nimitvijayvargee/keyboardv2/KICAD/keyboardv2.kicad_sch

## KiCad design KICAD/keyboardv2.kicad_sch (2025-06-17)

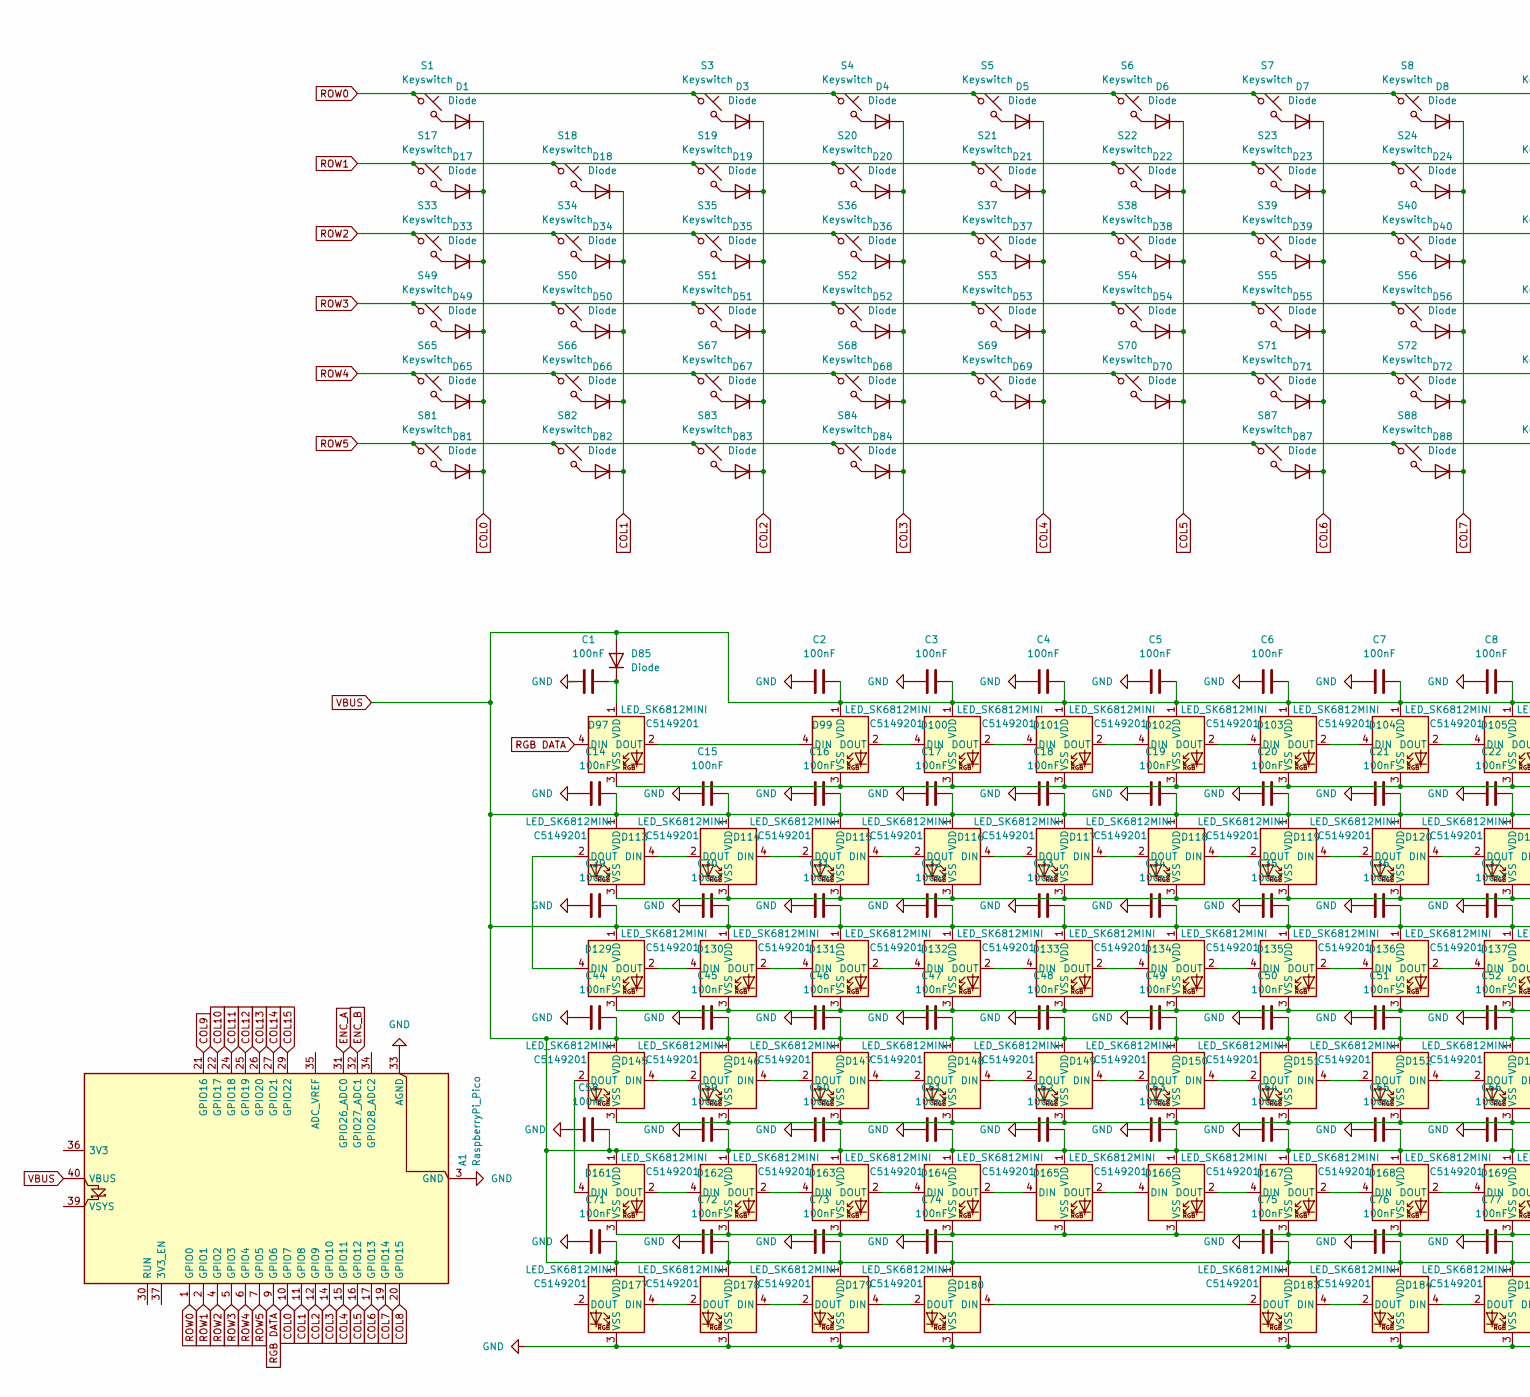
[picture p3: schematic keyboardv2.kicad_sch, part in row 1, column 1]

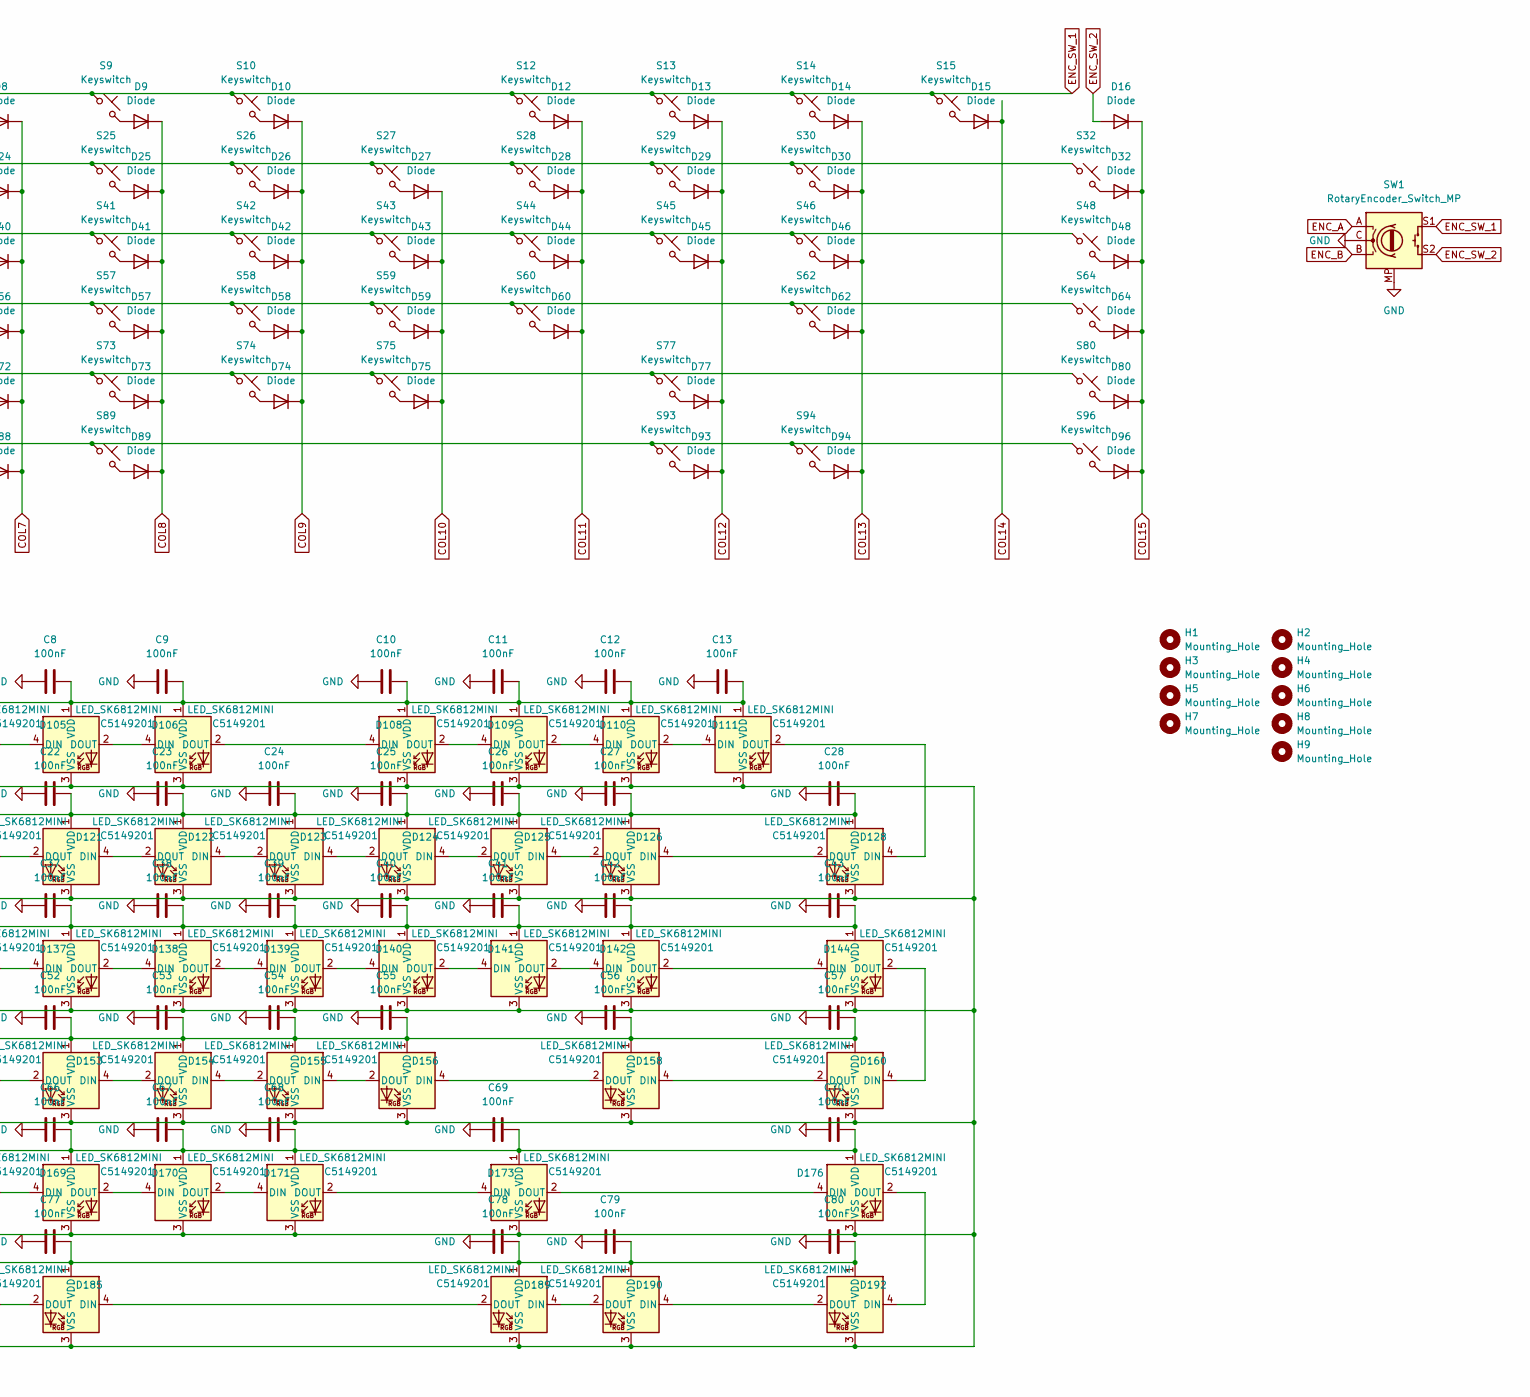
[picture p4: schematic keyboardv2.kicad_sch, part in row 1, column 2]

Parts:
A1: RaspberryPi_Pico; RaspberryPi_Pico_Common_Unspecified
C1, C2, C3, C4, C5, C6, C7, C8, C9, C10, C11, C12, C13, C14, C15, C16, C17, C18, C19, C20, C21, C22, C23, C24, C25, C26, C27, C28, C29, C30, C31, C32, C33, C34, C35, C36, C37, C38, C39, C40, C41, C42, C43, C44, C45, C46, C47, C48, C49, C50, C51, C52, C53, C54, C55, C56, C57, C58, C59, C60, C61, C62, C63, C64, C65, C66, C67, C68, C69, C70, C71, C72, C73, C74, C75, C76, C77, C78, C79, C80: 100nF; C_0402_1005Metric
D1, D3, D4, D5, D6, D7, D8, D9, D10, D12, D13, D14, D15, D16, D17, D18, D19, D20, D21, D22, D23, D24, D25, D26, D27, D28, D29, D30, D32, D33, D34, D35, D36, D37, D38, D39, D40, D41, D42, D43, D44, D45, D46, D48, D49, D50, D51, D52, D53, D54, D55, D56, D57, D58, D59, D60, D62, D64, D65, D66, D67, D68, D69, D70, D71, D72, D73, D74, D75, D77, D80, D81, D82, D83, D84, D85, D87, D88, D89, D93, D94, D96: Diode; D_SOD-123
D97, D99, D100, D101, D102, D103, D104, D105, D106, D108, D109, D110, D111, D113, D114, D115, D116, D117, D118, D119, D120, D121, D122, D123, D124, D125, D126, D128, D129, D130, D131, D132, D133, D134, D135, D136, D137, D138, D139, D140, D141, D142, D144, D145, D146, D147, D148, D149, D150, D151, D152, D153, D154, D155, D156, D158, D160, D161, D162, D163, D164, D165, D166, D167, D168, D169, D170, D171, D173, D176, D177, D178, D179, D180, D183, D184, D185, D189, D190, D192: LED_SK6812MINI; LED_SK6812-E; LCSC C5149201
H1, H2, H3: Mounting_Hole; Stabilizer_MX_2.00u
H4: Mounting_Hole; Stabilizer_MX_6.25u
H5, H6, H7, H8, H9: Mounting_Hole; MountingHole_3.2mm_M3
S1, S3, S4, S5, S6, S7, S8, S9, S10, S12, S13, S14, S15, S17, S18, S19, S20, S21, S22, S23, S24, S25, S26, S27, S28, S29, S32, S34, S35, S36, S37, S38, S39, S40, S41, S42, S43, S44, S45, S48, S50, S51, S52, S53, S54, S55, S56, S57, S58, S59, S60, S64, S66, S67, S68, S69, S70, S71, S72, S73, S74, S75, S80, S89, S93, S94, S96: Keyswitch; MX_PCB_1.00u
S30: Keyswitch; MX_PCB_2.00u
S33, S46: Keyswitch; MX_PCB_1.50u
S49, S77: Keyswitch; MX_PCB_1.75u
S62, S65: Keyswitch; MX_PCB_2.25u
S81, S82, S83, S87, S88: Keyswitch; MX_PCB_1.25u
S84: Keyswitch; MX_PCB_6.25u
SW1: RotaryEncoder_Switch_MP; RotaryEncoder_Alps_EC11E-Switch_Vertical_H20mm_MountingHoles

Connections:
COL0: A1.10 (GPIO7), D1.1 (K), D17.1 (K), D33.1 (K), D49.1 (K), D65.1 (K), D81.1 (K)
COL1: A1.11 (GPIO8), D18.1 (K), D34.1 (K), D50.1 (K), D66.1 (K), D82.1 (K)
COL2: A1.12 (GPIO9), D3.1 (K), D19.1 (K), D35.1 (K), D51.1 (K), D67.1 (K), D83.1 (K)
COL3: A1.14 (GPIO10), D4.1 (K), D20.1 (K), D36.1 (K), D52.1 (K), D68.1 (K), D84.1 (K)
COL4: A1.15 (GPIO11), D5.1 (K), D21.1 (K), D37.1 (K), D53.1 (K), D69.1 (K)
COL5: A1.16 (GPIO12), D6.1 (K), D22.1 (K), D38.1 (K), D54.1 (K), D70.1 (K)
COL6: A1.17 (GPIO13), D7.1 (K), D23.1 (K), D39.1 (K), D55.1 (K), D71.1 (K), D87.1 (K)
COL7: A1.19 (GPIO14), D8.1 (K), D24.1 (K), D40.1 (K), D56.1 (K), D72.1 (K), D88.1 (K)
COL8: A1.20 (GPIO15), D9.1 (K), D25.1 (K), D41.1 (K), D57.1 (K), D73.1 (K), D89.1 (K)
COL9: A1.21 (GPIO16), D10.1 (K), D26.1 (K), D42.1 (K), D58.1 (K), D74.1 (K)
COL10: A1.22 (GPIO17), D27.1 (K), D43.1 (K), D59.1 (K), D75.1 (K)
COL11: A1.24 (GPIO18), D12.1 (K), D28.1 (K), D44.1 (K), D60.1 (K)
COL12: A1.25 (GPIO19), D13.1 (K), D29.1 (K), D45.1 (K), D77.1 (K), D93.1 (K)
COL13: A1.26 (GPIO20), D14.1 (K), D30.1 (K), D46.1 (K), D62.1 (K), D94.1 (K)
COL14: A1.27 (GPIO21), D15.1 (K)
COL15: A1.29 (GPIO22), D16.1 (K), D32.1 (K), D48.1 (K), D64.1 (K), D80.1 (K), D96.1 (K)
ENC_A: A1.31 (GPIO26_ADC0), SW1.A
ENC_B: A1.32 (GPIO27_ADC1), SW1.B
ENC_SW_1: A1.1 (GPIO0), S1.1, S3.1, S4.1, S5.1, S6.1, S7.1, S8.1, S9.1, S10.1, S12.1, S13.1, S14.1, S15.1, SW1.S1
ENC_SW_2: D16.2 (A), SW1.S2
GND: A1.3 (GND), A1.8 (GND), A1.13 (GND), A1.18 (GND), A1.23 (GND), A1.28 (GND), A1.33 (AGND), A1.38 (GND), C1.1, C2.1, C3.1, C4.1, C5.1, C6.1, C7.1, C8.1, C9.1, C10.1, C11.1, C12.1, C13.1, C14.1, C15.1, C16.1, C17.1, C18.1, C19.1, C20.1, C21.1, C22.1, C23.1, C24.1, C25.1, C26.1, C27.1, C28.1, C29.1, C30.1, C31.1, C32.1, C33.1, C34.1, C35.1, C36.1, C37.1, C38.1, C39.1, C40.1, C41.1, C42.1, C43.1, C44.1, C45.1, C46.1, C47.1, C48.1, C49.1, C50.1, C51.1, C52.1, C53.1, C54.1, C55.1, C56.1, C57.1, C58.1, C59.1, C60.1, C61.1, C62.1, C63.1, C64.1, C65.1, C66.1, C67.1, C68.1, C69.1, C70.1, C71.1, C72.1, C73.1, C74.1, C75.1, C76.1, C77.1, C78.1, C79.1, C80.1, D97.3 (VSS), D99.3 (VSS), D100.3 (VSS), D101.3 (VSS), D102.3 (VSS), D103.3 (VSS), D104.3 (VSS), D105.3 (VSS), D106.3 (VSS), D108.3 (VSS), D109.3 (VSS), D110.3 (VSS), D111.3 (VSS), D113.3 (VSS), D114.3 (VSS), D115.3 (VSS), D116.3 (VSS), D117.3 (VSS), D118.3 (VSS), D119.3 (VSS), D120.3 (VSS), D121.3 (VSS), D122.3 (VSS), D123.3 (VSS), D124.3 (VSS), D125.3 (VSS), D126.3 (VSS), D128.3 (VSS), D129.3 (VSS), D130.3 (VSS), D131.3 (VSS), D132.3 (VSS), D133.3 (VSS), D134.3 (VSS), D135.3 (VSS), D136.3 (VSS), D137.3 (VSS), D138.3 (VSS), D139.3 (VSS), D140.3 (VSS), D141.3 (VSS), D142.3 (VSS), D144.3 (VSS), D145.3 (VSS), D146.3 (VSS), D147.3 (VSS), D148.3 (VSS), D149.3 (VSS), D150.3 (VSS), D151.3 (VSS), D152.3 (VSS), D153.3 (VSS), D154.3 (VSS), D155.3 (VSS), D156.3 (VSS), D158.3 (VSS), D160.3 (VSS), D161.3 (VSS), D162.3 (VSS), D163.3 (VSS), D164.3 (VSS), D165.3 (VSS), D166.3 (VSS), D167.3 (VSS), D168.3 (VSS), D169.3 (VSS), D170.3 (VSS), D171.3 (VSS), D173.3 (VSS), D176.3 (VSS), D177.3 (VSS), D178.3 (VSS), D179.3 (VSS), D180.3 (VSS), D183.3 (VSS), D184.3 (VSS), D185.3 (VSS), D189.3 (VSS), D190.3 (VSS), D192.3 (VSS), SW1.C, SW1.MP
unnamed: C1.2, D85.1 (K), D97.1 (VDD)
unnamed: D1.2 (A), S1.2
unnamed: D3.2 (A), S3.2
unnamed: D4.2 (A), S4.2
unnamed: D5.2 (A), S5.2
unnamed: D6.2 (A), S6.2
unnamed: D7.2 (A), S7.2
unnamed: D8.2 (A), S8.2
unnamed: D9.2 (A), S9.2
unnamed: D10.2 (A), S10.2
unnamed: D12.2 (A), S12.2
unnamed: D13.2 (A), S13.2
unnamed: D14.2 (A), S14.2
unnamed: D15.2 (A), S15.2
unnamed: D17.2 (A), S17.2
unnamed: D18.2 (A), S18.2
unnamed: D19.2 (A), S19.2
unnamed: D20.2 (A), S20.2
unnamed: D21.2 (A), S21.2
unnamed: D22.2 (A), S22.2
unnamed: D23.2 (A), S23.2
unnamed: D24.2 (A), S24.2
unnamed: D25.2 (A), S25.2
unnamed: D26.2 (A), S26.2
unnamed: D27.2 (A), S27.2
unnamed: D28.2 (A), S28.2
unnamed: D29.2 (A), S29.2
unnamed: D30.2 (A), S30.2
unnamed: D32.2 (A), S32.2
unnamed: D33.2 (A), S33.2
unnamed: D34.2 (A), S34.2
unnamed: D35.2 (A), S35.2
unnamed: D36.2 (A), S36.2
unnamed: D37.2 (A), S37.2
unnamed: D38.2 (A), S38.2
unnamed: D39.2 (A), S39.2
unnamed: D40.2 (A), S40.2
unnamed: D41.2 (A), S41.2
unnamed: D42.2 (A), S42.2
unnamed: D43.2 (A), S43.2
unnamed: D44.2 (A), S44.2
unnamed: D45.2 (A), S45.2
unnamed: D46.2 (A), S46.2
unnamed: D48.2 (A), S48.2
unnamed: D49.2 (A), S49.2
unnamed: D50.2 (A), S50.2
unnamed: D51.2 (A), S51.2
unnamed: D52.2 (A), S52.2
unnamed: D53.2 (A), S53.2
unnamed: D54.2 (A), S54.2
unnamed: D55.2 (A), S55.2
unnamed: D56.2 (A), S56.2
unnamed: D57.2 (A), S57.2
unnamed: D58.2 (A), S58.2
unnamed: D59.2 (A), S59.2
unnamed: D60.2 (A), S60.2
unnamed: D62.2 (A), S62.2
unnamed: D64.2 (A), S64.2
unnamed: D65.2 (A), S65.2
unnamed: D66.2 (A), S66.2
unnamed: D67.2 (A), S67.2
unnamed: D68.2 (A), S68.2
unnamed: D69.2 (A), S69.2
unnamed: D70.2 (A), S70.2
unnamed: D71.2 (A), S71.2
unnamed: D72.2 (A), S72.2
unnamed: D73.2 (A), S73.2
unnamed: D74.2 (A), S74.2
unnamed: D75.2 (A), S75.2
unnamed: D77.2 (A), S77.2
unnamed: D80.2 (A), S80.2
unnamed: D81.2 (A), S81.2
unnamed: D82.2 (A), S82.2
unnamed: D83.2 (A), S83.2
unnamed: D84.2 (A), S84.2
unnamed: D87.2 (A), S87.2
unnamed: D88.2 (A), S88.2
unnamed: D89.2 (A), S89.2
unnamed: D93.2 (A), S93.2
unnamed: D94.2 (A), S94.2
unnamed: D96.2 (A), S96.2
unnamed: D97.2 (DOUT), D99.4 (DIN)
unnamed: D100.2 (DOUT), D101.4 (DIN)
unnamed: D99.2 (DOUT), D100.4 (DIN)
unnamed: D101.2 (DOUT), D102.4 (DIN)
unnamed: D102.2 (DOUT), D103.4 (DIN)
unnamed: D103.2 (DOUT), D104.4 (DIN)
unnamed: D104.2 (DOUT), D105.4 (DIN)
unnamed: D105.2 (DOUT), D106.4 (DIN)
unnamed: D106.2 (DOUT), D108.4 (DIN)
unnamed: D108.2 (DOUT), D109.4 (DIN)
unnamed: D109.2 (DOUT), D110.4 (DIN)
unnamed: D110.2 (DOUT), D111.4 (DIN)
unnamed: D111.2 (DOUT), D128.4 (DIN)
unnamed: D113.2 (DOUT), D129.4 (DIN)
unnamed: D113.4 (DIN), D114.2 (DOUT)
unnamed: D114.4 (DIN), D115.2 (DOUT)
unnamed: D115.4 (DIN), D116.2 (DOUT)
unnamed: D116.4 (DIN), D117.2 (DOUT)
unnamed: D117.4 (DIN), D118.2 (DOUT)
unnamed: D118.4 (DIN), D119.2 (DOUT)
unnamed: D119.4 (DIN), D120.2 (DOUT)
unnamed: D120.4 (DIN), D121.2 (DOUT)
unnamed: D121.4 (DIN), D122.2 (DOUT)
unnamed: D122.4 (DIN), D123.2 (DOUT)
unnamed: D123.4 (DIN), D124.2 (DOUT)
unnamed: D124.4 (DIN), D125.2 (DOUT)
unnamed: D125.4 (DIN), D126.2 (DOUT)
unnamed: D126.4 (DIN), D128.2 (DOUT)
unnamed: D129.2 (DOUT), D130.4 (DIN)
unnamed: D130.2 (DOUT), D131.4 (DIN)
unnamed: D131.2 (DOUT), D132.4 (DIN)
unnamed: D132.2 (DOUT), D133.4 (DIN)
unnamed: D133.2 (DOUT), D134.4 (DIN)
unnamed: D134.2 (DOUT), D135.4 (DIN)
unnamed: D135.2 (DOUT), D136.4 (DIN)
unnamed: D136.2 (DOUT), D137.4 (DIN)
unnamed: D137.2 (DOUT), D138.4 (DIN)
unnamed: D138.2 (DOUT), D139.4 (DIN)
unnamed: D139.2 (DOUT), D140.4 (DIN)
unnamed: D140.2 (DOUT), D141.4 (DIN)
unnamed: D141.2 (DOUT), D142.4 (DIN)
unnamed: D142.2 (DOUT), D144.4 (DIN)
unnamed: D144.2 (DOUT), D160.4 (DIN)
unnamed: D145.2 (DOUT), D161.4 (DIN)
unnamed: D145.4 (DIN), D146.2 (DOUT)
unnamed: D146.4 (DIN), D147.2 (DOUT)
unnamed: D147.4 (DIN), D148.2 (DOUT)
unnamed: D148.4 (DIN), D149.2 (DOUT)
unnamed: D149.4 (DIN), D150.2 (DOUT)
unnamed: D150.4 (DIN), D151.2 (DOUT)
unnamed: D151.4 (DIN), D152.2 (DOUT)
unnamed: D152.4 (DIN), D153.2 (DOUT)
unnamed: D153.4 (DIN), D154.2 (DOUT)
unnamed: D154.4 (DIN), D155.2 (DOUT)
unnamed: D155.4 (DIN), D156.2 (DOUT)
unnamed: D156.4 (DIN), D158.2 (DOUT)
unnamed: D158.4 (DIN), D160.2 (DOUT)
unnamed: D161.2 (DOUT), D162.4 (DIN)
unnamed: D162.2 (DOUT), D163.4 (DIN)
unnamed: D163.2 (DOUT), D164.4 (DIN)
unnamed: D164.2 (DOUT), D165.4 (DIN)
unnamed: D165.2 (DOUT), D166.4 (DIN)
unnamed: D166.2 (DOUT), D167.4 (DIN)
unnamed: D167.2 (DOUT), D168.4 (DIN)
unnamed: D168.2 (DOUT), D169.4 (DIN)
unnamed: D169.2 (DOUT), D170.4 (DIN)
unnamed: D170.2 (DOUT), D171.4 (DIN)
unnamed: D171.2 (DOUT), D173.4 (DIN)
unnamed: D173.2 (DOUT), D176.4 (DIN)
unnamed: D176.2 (DOUT), D192.4 (DIN)
unnamed: D177.4 (DIN), D178.2 (DOUT)
unnamed: D178.4 (DIN), D179.2 (DOUT)
unnamed: D179.4 (DIN), D180.2 (DOUT)
unnamed: D180.4 (DIN), D183.2 (DOUT)
unnamed: D183.4 (DIN), D184.2 (DOUT)
unnamed: D184.4 (DIN), D185.2 (DOUT)
unnamed: D185.4 (DIN), D189.2 (DOUT)
unnamed: D189.4 (DIN), D190.2 (DOUT)
unnamed: D190.4 (DIN), D192.2 (DOUT)
RGB DATA: A1.9 (GPIO6), D97.4 (DIN)
ROW1: A1.2 (GPIO1), S17.1, S18.1, S19.1, S20.1, S21.1, S22.1, S23.1, S24.1, S25.1, S26.1, S27.1, S28.1, S29.1, S30.1, S32.1
ROW2: A1.4 (GPIO2), S33.1, S34.1, S35.1, S36.1, S37.1, S38.1, S39.1, S40.1, S41.1, S42.1, S43.1, S44.1, S45.1, S46.1, S48.1
ROW3: A1.5 (GPIO3), S49.1, S50.1, S51.1, S52.1, S53.1, S54.1, S55.1, S56.1, S57.1, S58.1, S59.1, S60.1, S62.1, S64.1
ROW4: A1.6 (GPIO4), S65.1, S66.1, S67.1, S68.1, S69.1, S70.1, S71.1, S72.1, S73.1, S74.1, S75.1, S77.1, S80.1
ROW5: A1.7 (GPIO5), S81.1, S82.1, S83.1, S84.1, S87.1, S88.1, S89.1, S93.1, S94.1, S96.1
VBUS: A1.40 (VBUS), C2.2, C3.2, C4.2, C5.2, C6.2, C7.2, C8.2, C9.2, C10.2, C11.2, C12.2, C13.2, C14.2, C15.2, C16.2, C17.2, C18.2, C19.2, C20.2, C21.2, C22.2, C23.2, C24.2, C25.2, C26.2, C27.2, C28.2, C29.2, C30.2, C31.2, C32.2, C33.2, C34.2, C35.2, C36.2, C37.2, C38.2, C39.2, C40.2, C41.2, C42.2, C43.2, C44.2, C45.2, C46.2, C47.2, C48.2, C49.2, C50.2, C51.2, C52.2, C53.2, C54.2, C55.2, C56.2, C57.2, C58.2, C59.2, C60.2, C61.2, C62.2, C63.2, C64.2, C65.2, C66.2, C67.2, C68.2, C69.2, C70.2, C71.2, C72.2, C73.2, C74.2, C75.2, C76.2, C77.2, C78.2, C79.2, C80.2, D85.2 (A), D99.1 (VDD), D100.1 (VDD), D101.1 (VDD), D102.1 (VDD), D103.1 (VDD), D104.1 (VDD), D105.1 (VDD), D106.1 (VDD), D108.1 (VDD), D109.1 (VDD), D110.1 (VDD), D111.1 (VDD), D113.1 (VDD), D114.1 (VDD), D115.1 (VDD), D116.1 (VDD), D117.1 (VDD), D118.1 (VDD), D119.1 (VDD), D120.1 (VDD), D121.1 (VDD), D122.1 (VDD), D123.1 (VDD), D124.1 (VDD), D125.1 (VDD), D126.1 (VDD), D128.1 (VDD), D129.1 (VDD), D130.1 (VDD), D131.1 (VDD), D132.1 (VDD), D133.1 (VDD), D134.1 (VDD), D135.1 (VDD), D136.1 (VDD), D137.1 (VDD), D138.1 (VDD), D139.1 (VDD), D140.1 (VDD), D141.1 (VDD), D142.1 (VDD), D144.1 (VDD), D145.1 (VDD), D146.1 (VDD), D147.1 (VDD), D148.1 (VDD), D149.1 (VDD), D150.1 (VDD), D151.1 (VDD), D152.1 (VDD), D153.1 (VDD), D154.1 (VDD), D155.1 (VDD), D156.1 (VDD), D158.1 (VDD), D160.1 (VDD), D161.1 (VDD), D162.1 (VDD), D163.1 (VDD), D164.1 (VDD), D165.1 (VDD), D166.1 (VDD), D167.1 (VDD), D168.1 (VDD), D169.1 (VDD), D170.1 (VDD), D171.1 (VDD), D173.1 (VDD), D176.1 (VDD), D177.1 (VDD), D178.1 (VDD), D179.1 (VDD), D180.1 (VDD), D183.1 (VDD), D184.1 (VDD), D185.1 (VDD), D189.1 (VDD), D190.1 (VDD), D192.1 (VDD)
